mhaphungpleng/rc-car/images/PID.png

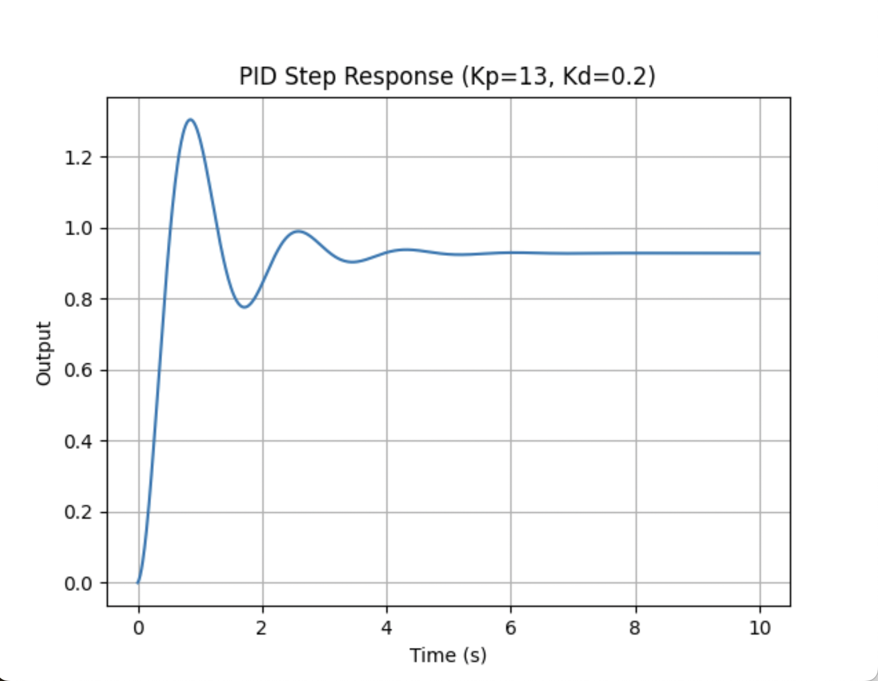
images/PID.png
