mhaphungpleng/rc-car/models/meshes/งาน6.jpg

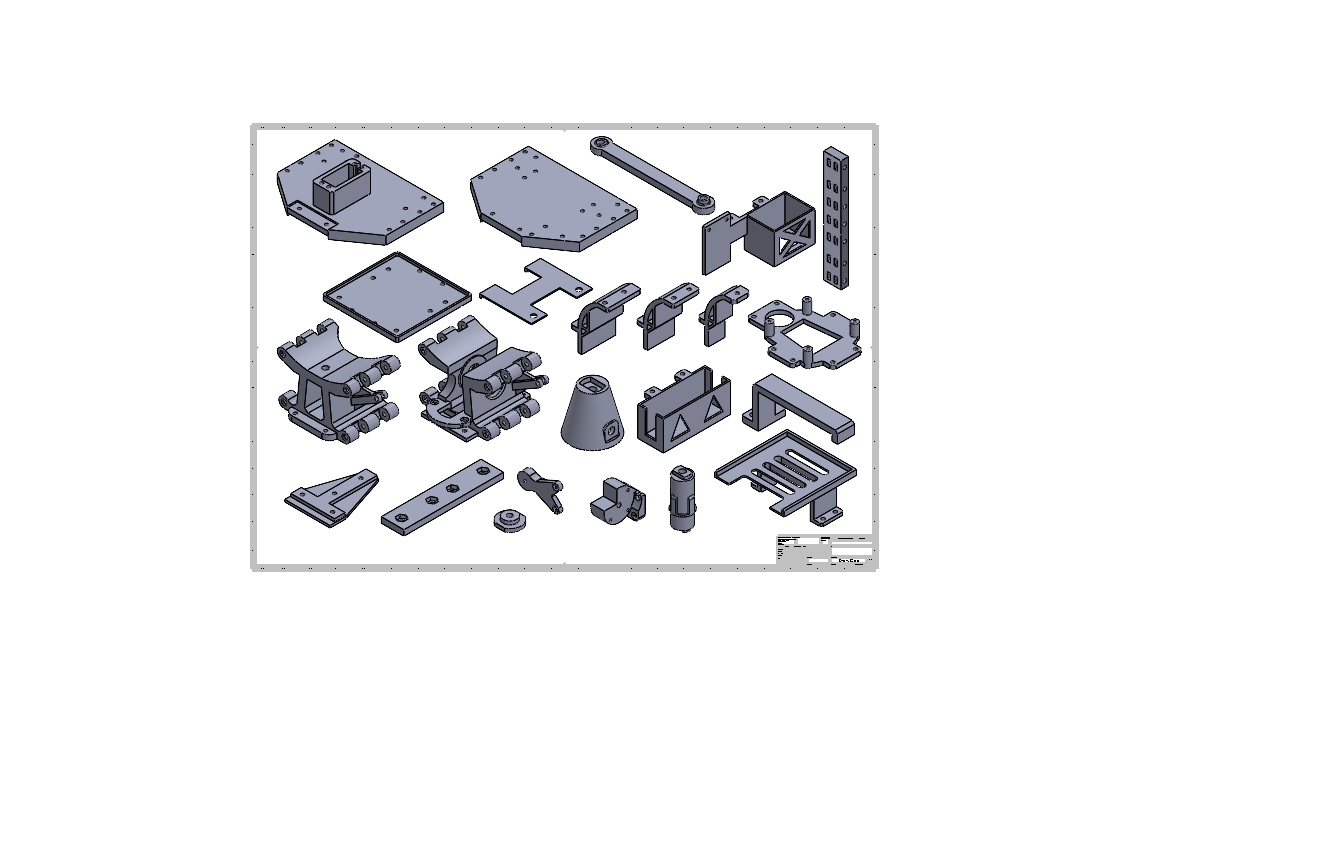
models/meshes/งาน6.jpg
