mhaphungpleng/rc-car/models/cad/BB_Base.SLDPRT

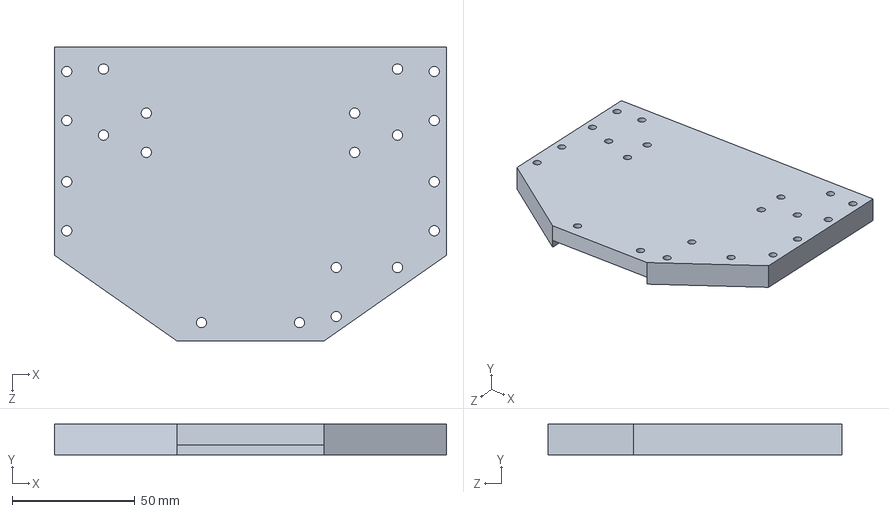
[picture p25: CAD file, 2026-02-09]
models/cad/BB_Base.SLDPRT
160.0 x 12.5 x 120.0 mm
