mhaphungpleng/rc-car/models/cad_stl/GearRccar46T.stl

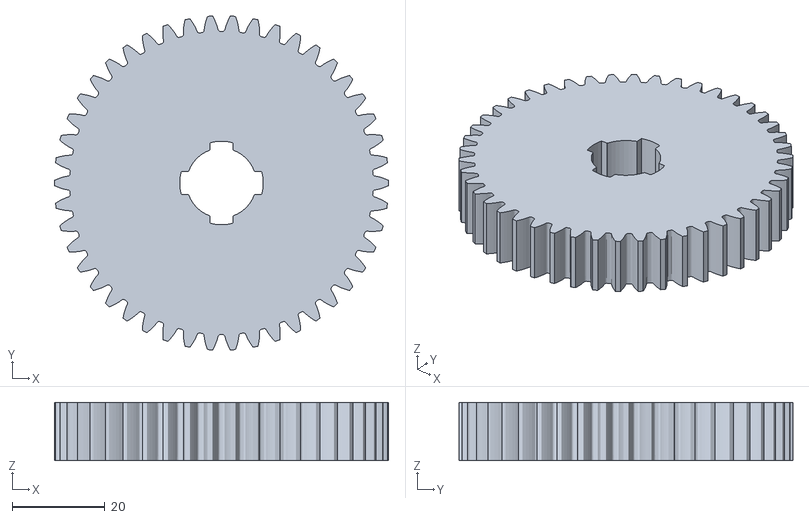
[picture p26: CAD file, 2026-02-09]
models/cad_stl/GearRccar46T.stl
72.0 x 71.9 x 12.5
