mhaphungpleng/rc-car/models/cad/Servohorn.SLDPRT

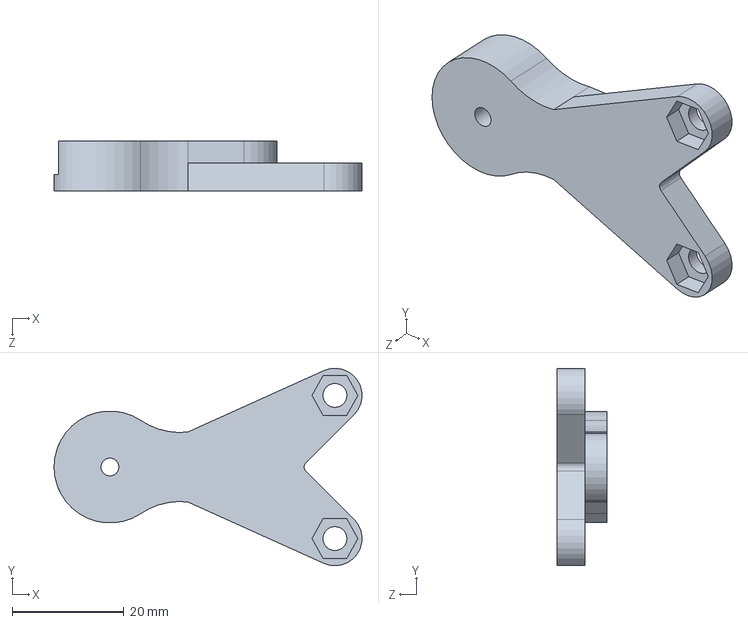
[picture p27: CAD file, 2026-02-09]
models/cad/Servohorn.SLDPRT
55.1 x 35.3 x 9.00 mm
