mhaphungpleng/rc-car/models/cad_stl/axle.stl

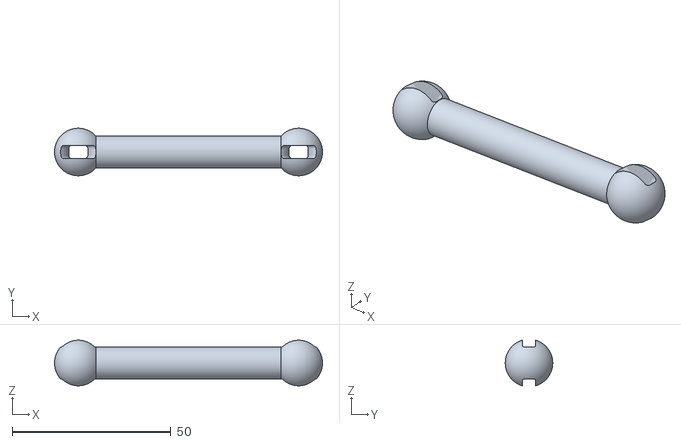
[picture p28: CAD file, 2026-02-09]
models/cad_stl/axle.stl
84.5 x 15.0 x 14.4
