mhaphungpleng/rc-car/models/cad/FFBody_to_Drive.SLDPRT

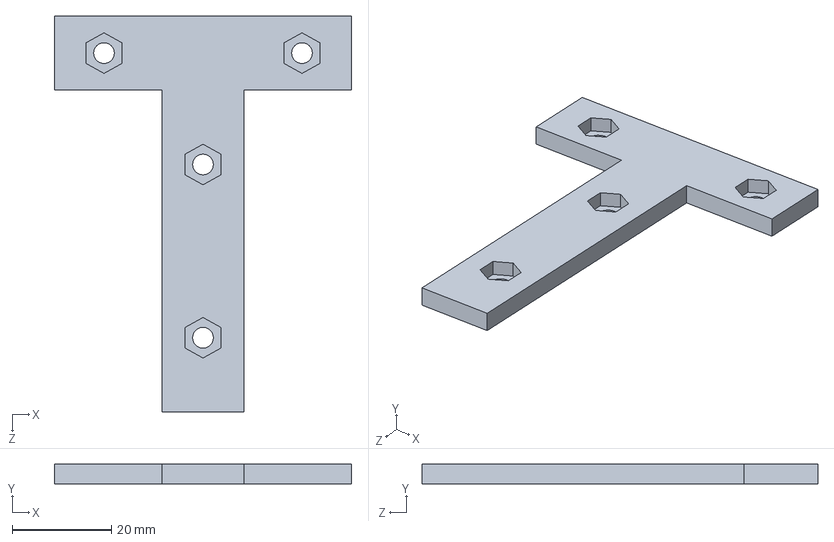
[picture p29: CAD file, 2026-02-09]
models/cad/FFBody_to_Drive.SLDPRT
60.0 x 4.00 x 80.0 mm
