mhaphungpleng/rc-car/models/cad_stl/rear_lower_fork_right.stl

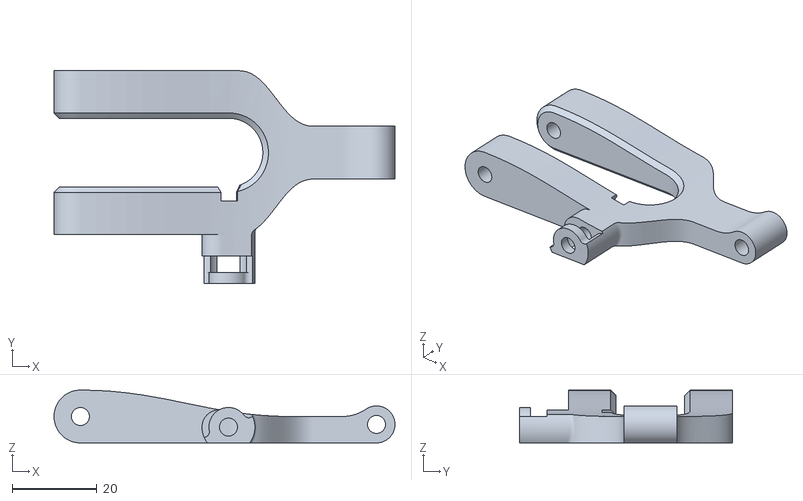
[picture p30: CAD file, 2026-02-09]
models/cad_stl/rear_lower_fork_right.stl
80.6 x 50.2 x 12.5
