mhaphungpleng/rc-car/models/cad/GearRccar52T.step

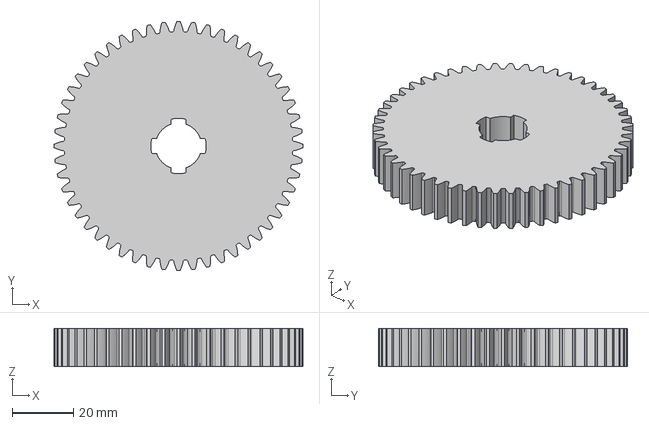
[picture p31: CAD file, 2026-02-09]
models/cad/GearRccar52T.step
81.0 x 81.0 x 12.5 mm
