mhaphungpleng/rc-car/models/cad_stl/SeizeFF.STL

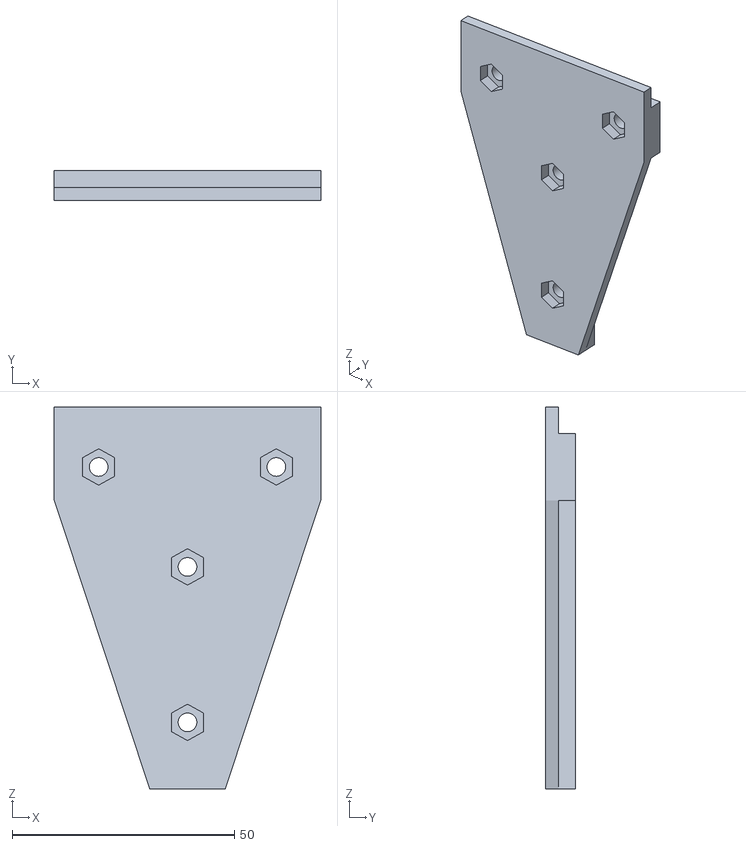
[picture p32: CAD file, 2026-02-09]
models/cad_stl/SeizeFF.STL
60.0 x 6.80 x 86.0
