mhaphungpleng/rc-car/models/cad/Futureboard.SLDPRT

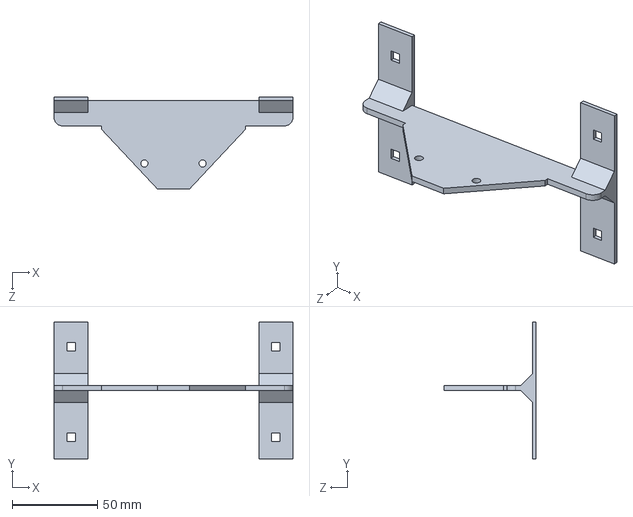
[picture p33: CAD file, 2026-02-09]
models/cad/Futureboard.SLDPRT
140.0 x 80.0 x 54.0 mm
