mhaphungpleng/rc-car/models/cad_stl/Drivengearaxel.STL

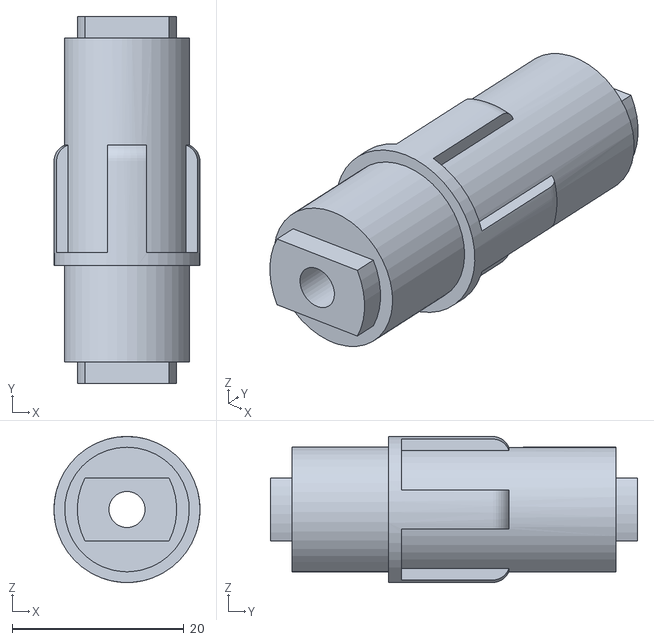
[picture p34: CAD file, 2026-02-09]
models/cad_stl/Drivengearaxel.STL
17.0 x 42.8 x 17.0
