mhaphungpleng/rc-car/models/cad/ServoarmV85.SLDPRT

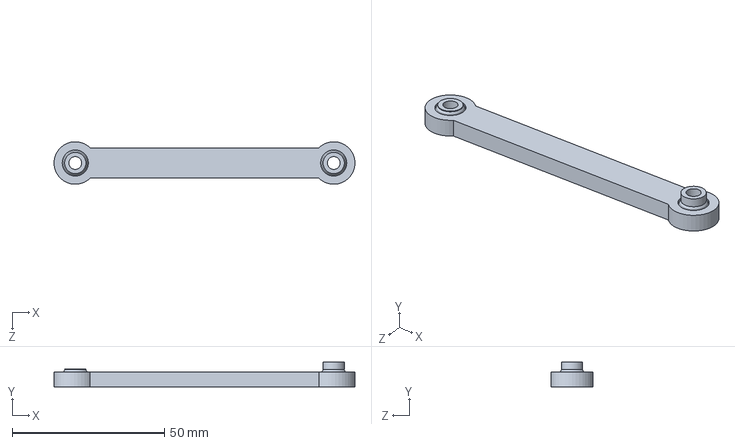
[picture p35: CAD file, 2026-02-09]
models/cad/ServoarmV85.SLDPRT
99.0 x 8.20 x 14.0 mm
