mhaphungpleng/rc-car/models/cad_stl/GearRccar42T.stl

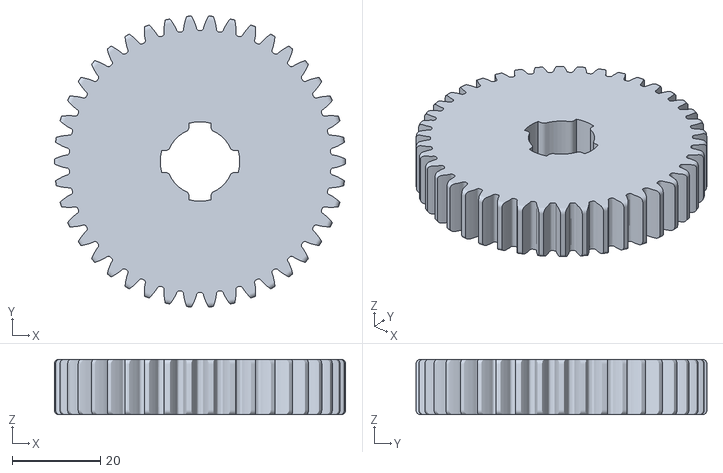
[picture p36: CAD file, 2026-02-09]
models/cad_stl/GearRccar42T.stl
66.0 x 65.9 x 12.5
