mhaphungpleng/rc-car/models/cad/LidarArmBack.SLDPRT

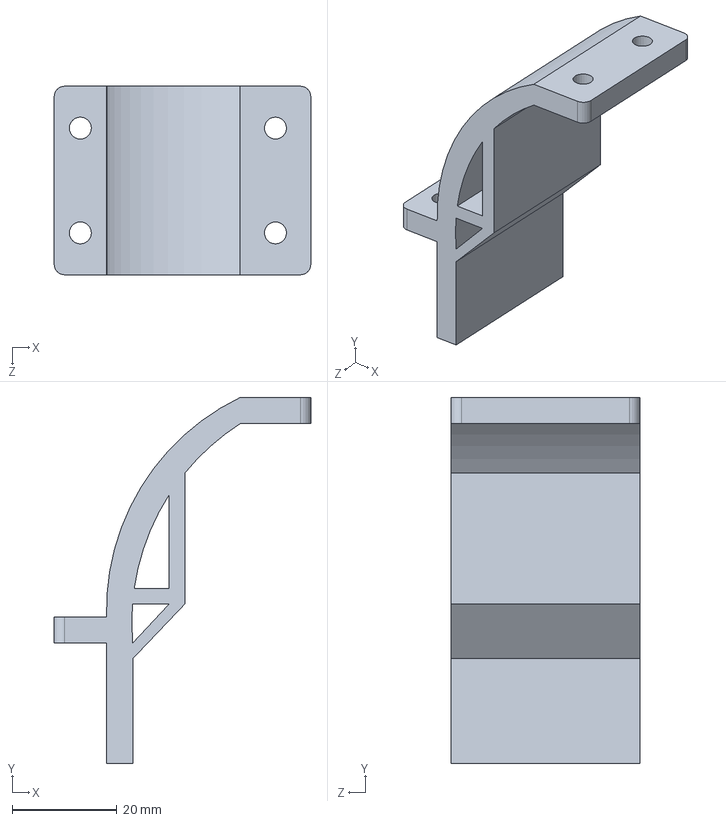
[picture p37: CAD file, 2026-02-09]
models/cad/LidarArmBack.SLDPRT
49.0 x 69.9 x 36.0 mm
