mhaphungpleng/rc-car/models/cad_stl/SeizeFHigh.STL

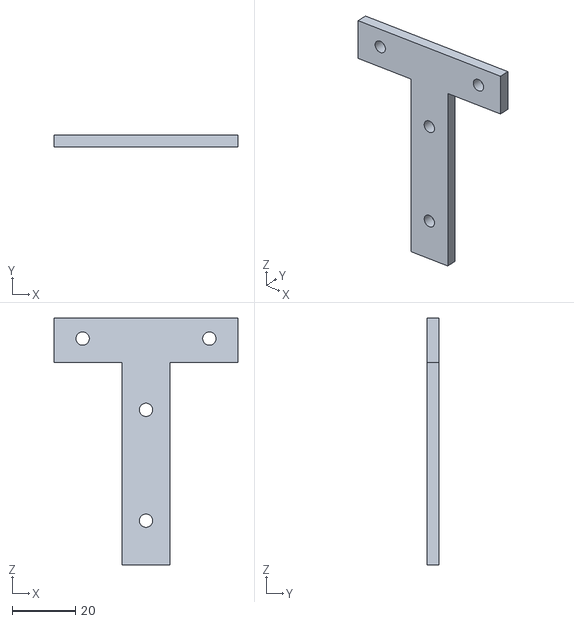
[picture p38: CAD file, 2026-02-09]
models/cad_stl/SeizeFHigh.STL
58.0 x 3.80 x 78.0
