mhaphungpleng/rc-car/models/cad/Box.SLDPRT

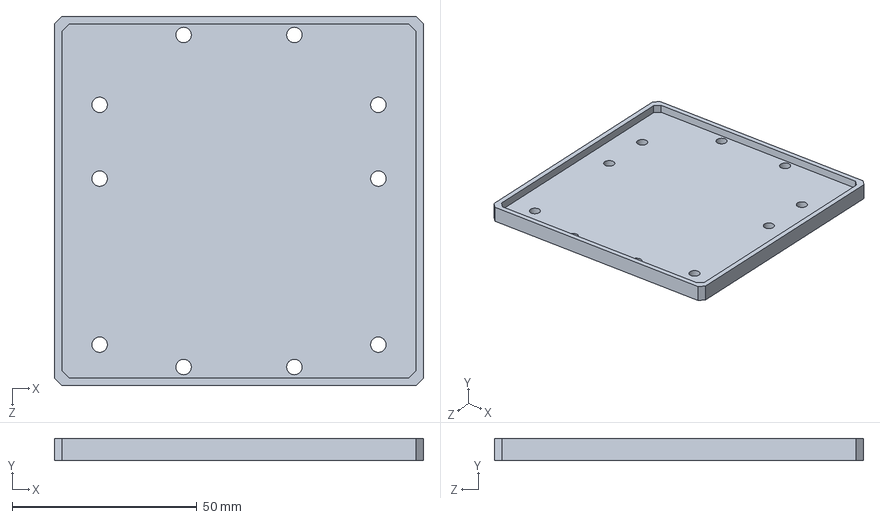
[picture p39: CAD file, 2026-02-09]
models/cad/Box.SLDPRT
100.0 x 6.00 x 100.0 mm
