mhaphungpleng/rc-car/models/cad_stl/Moter.STL

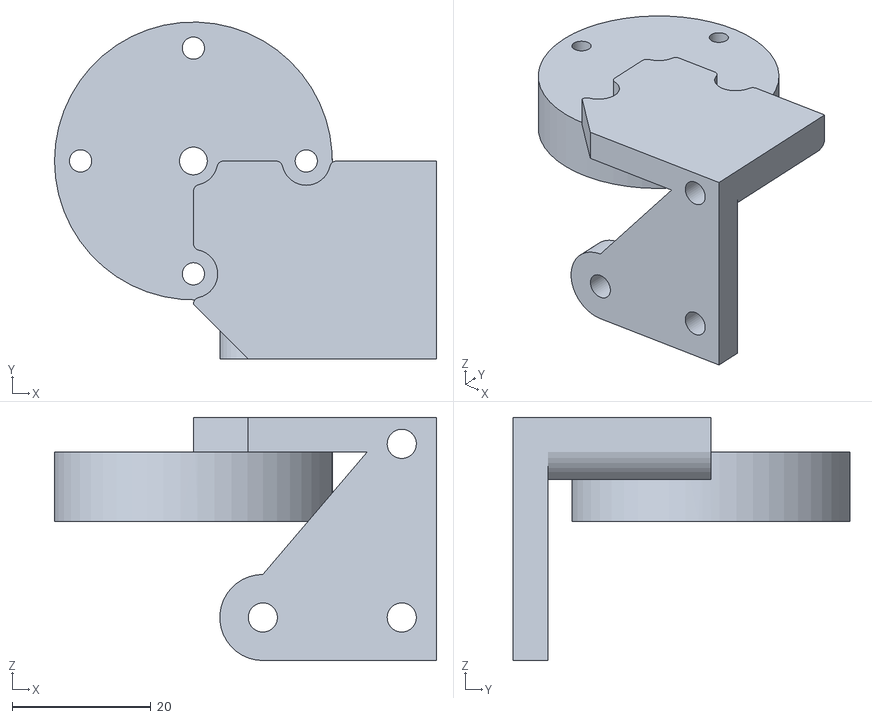
[picture p40: CAD file, 2026-02-09]
models/cad_stl/Moter.STL
55.0 x 48.5 x 35.0
