mhaphungpleng/rc-car/models/cad/Pi5_coverF.SLDPRT

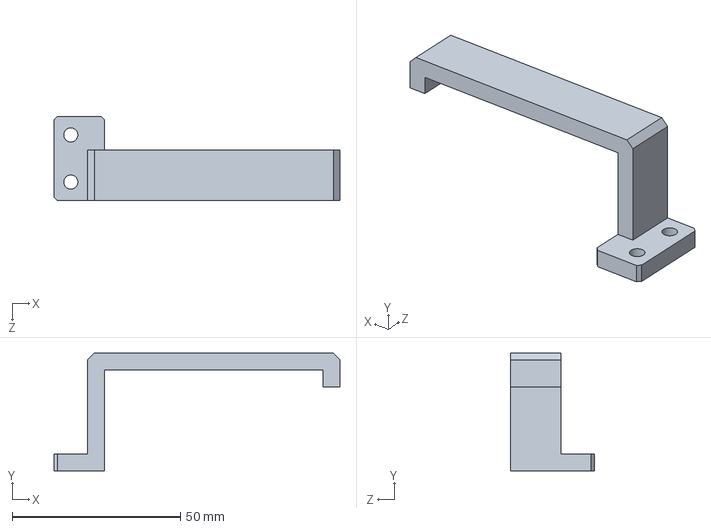
[picture p41: CAD file, 2026-02-09]
models/cad/Pi5_coverF.SLDPRT
85.0 x 35.0 x 25.0 mm
