mhaphungpleng/rc-car/models/cad_stl/ArmLidar.STL

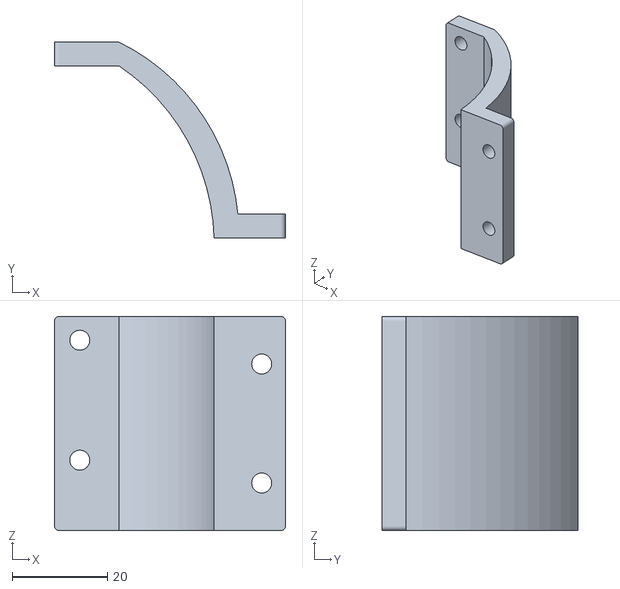
[picture p42: CAD file, 2026-02-09]
models/cad_stl/ArmLidar.STL
48.5 x 41.2 x 45.0
