mhaphungpleng/rc-car/models/cad_stl/Servoarm.STL

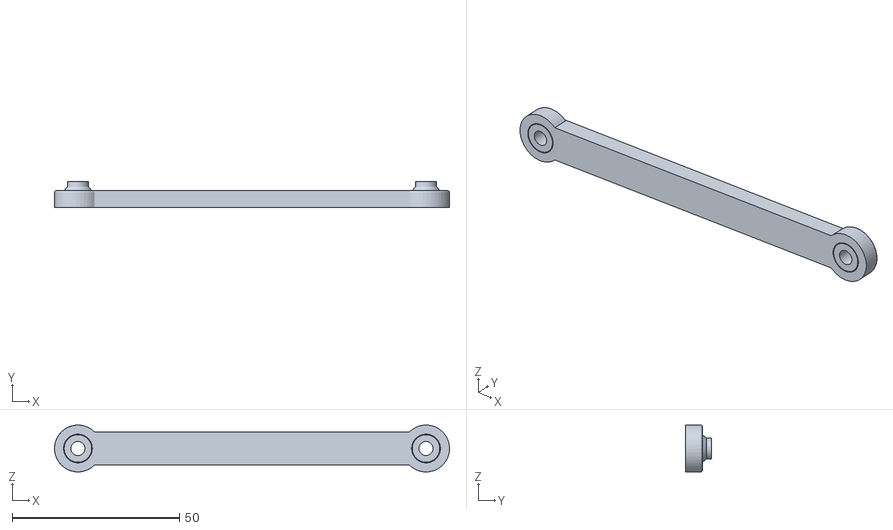
[picture p43: CAD file, 2026-02-09]
models/cad_stl/Servoarm.STL
118.0 x 7.71 x 14.0
