mhaphungpleng/rc-car/models/cad/Gyro.SLDPRT

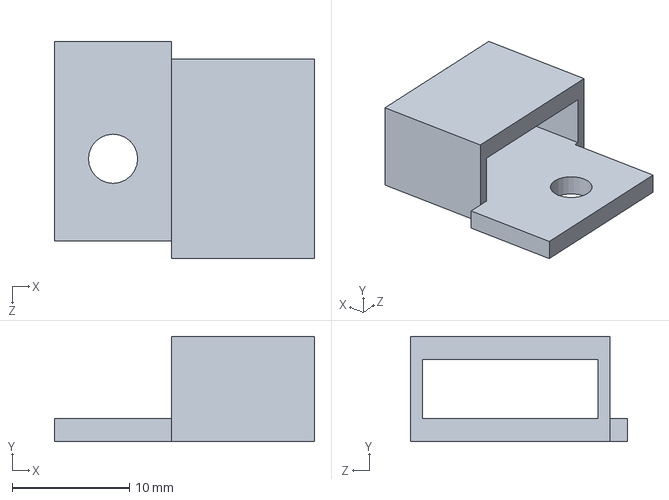
[picture p44: CAD file, 2026-02-09]
models/cad/Gyro.SLDPRT
22.2 x 9.00 x 18.5 mm
