mhaphungpleng/rc-car/models/cad_stl/rear_upper_fork.stl

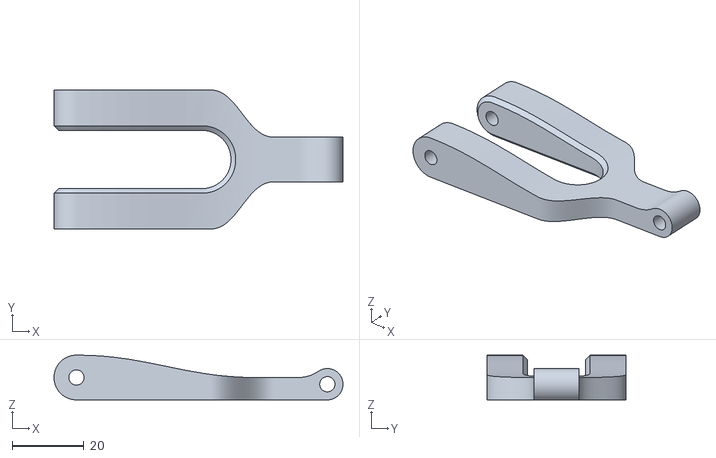
[picture p45: CAD file, 2026-02-09]
models/cad_stl/rear_upper_fork.stl
80.6 x 38.8 x 12.5
