mhaphungpleng/rc-car/models/cad/Wheel_grap6anglemm.SLDPRT

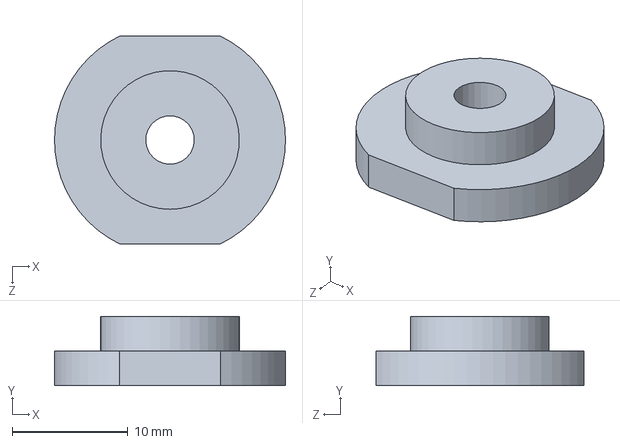
[picture p46: CAD file, 2026-02-09]
models/cad/Wheel_grap6anglemm.SLDPRT
20.0 x 6.00 x 18.0 mm
