mhaphungpleng/rc-car/models/cad_stl/SeizeB.STL

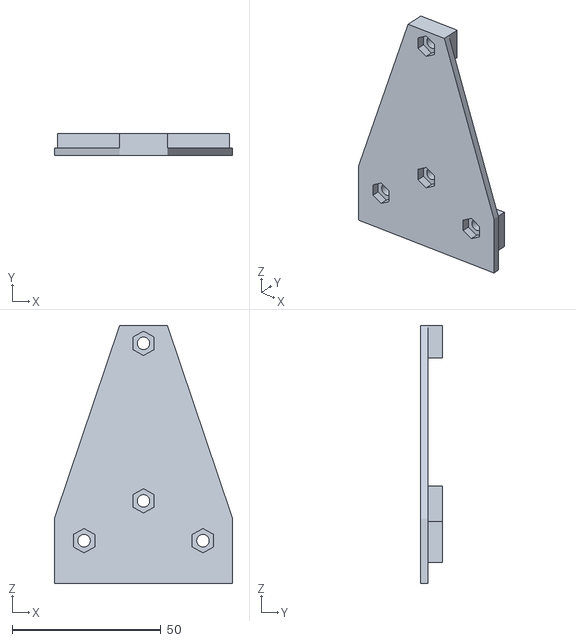
[picture p47: CAD file, 2026-02-09]
models/cad_stl/SeizeB.STL
60.0 x 7.30 x 86.8
