mhaphungpleng/rc-car/models/cad/SpoilerCover.SLDPRT

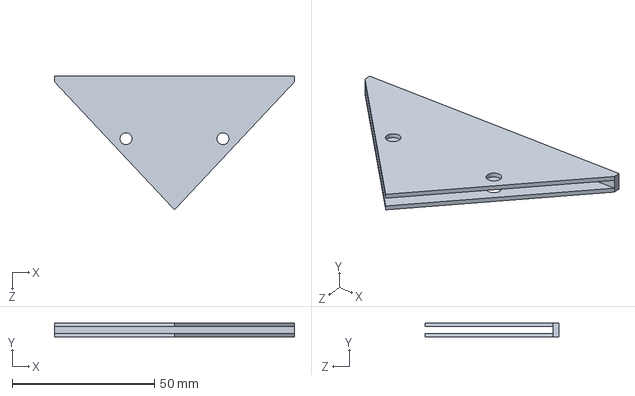
[picture p48: CAD file, 2026-02-09]
models/cad/SpoilerCover.SLDPRT
84.3 x 4.80 x 47.0 mm
