mhaphungpleng/rc-car/models/cad/Spoiler.SLDPRT

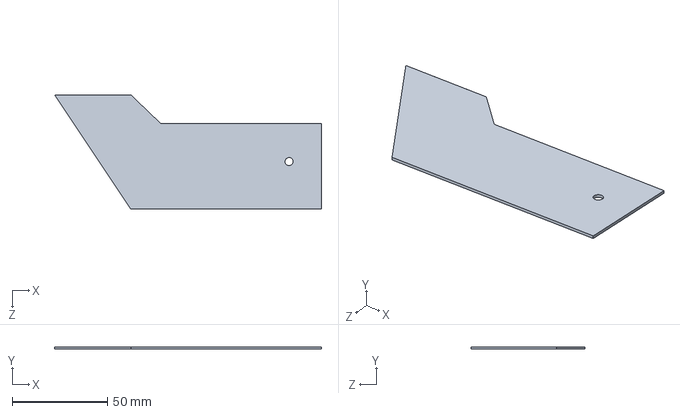
[picture p49: CAD file, 2026-02-09]
models/cad/Spoiler.SLDPRT
140.0 x 1.20 x 60.0 mm
