mhaphungpleng/rc-car/models/cad/BatteryV2.SLDPRT

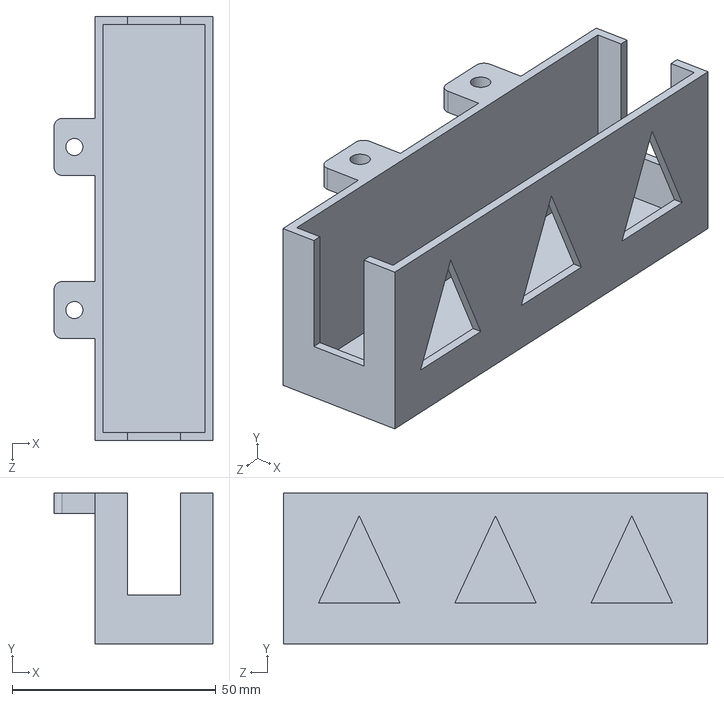
[picture p50: CAD file, 2026-02-09]
models/cad/BatteryV2.SLDPRT
39.0 x 37.0 x 104.0 mm
