mhaphungpleng/rc-car/models/cad/LidarArmR.SLDPRT

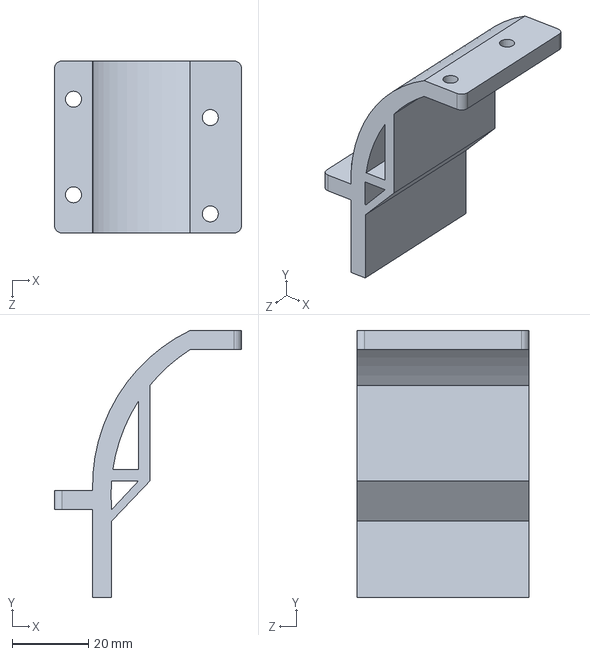
[picture p51: CAD file, 2026-02-09]
models/cad/LidarArmR.SLDPRT
49.0 x 69.9 x 45.0 mm
