mhaphungpleng/rc-car/models/cad/Driven_axel.SLDPRT

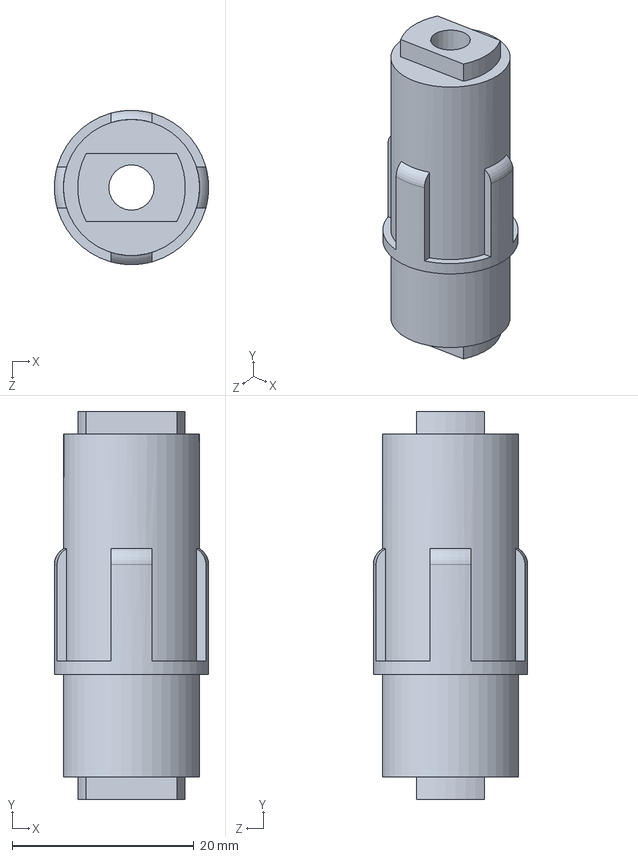
[picture p52: CAD file, 2026-02-09]
models/cad/Driven_axel.SLDPRT
17.0 x 42.8 x 17.0 mm
