mhaphungpleng/rc-car/models/cad/Battery.SLDPRT

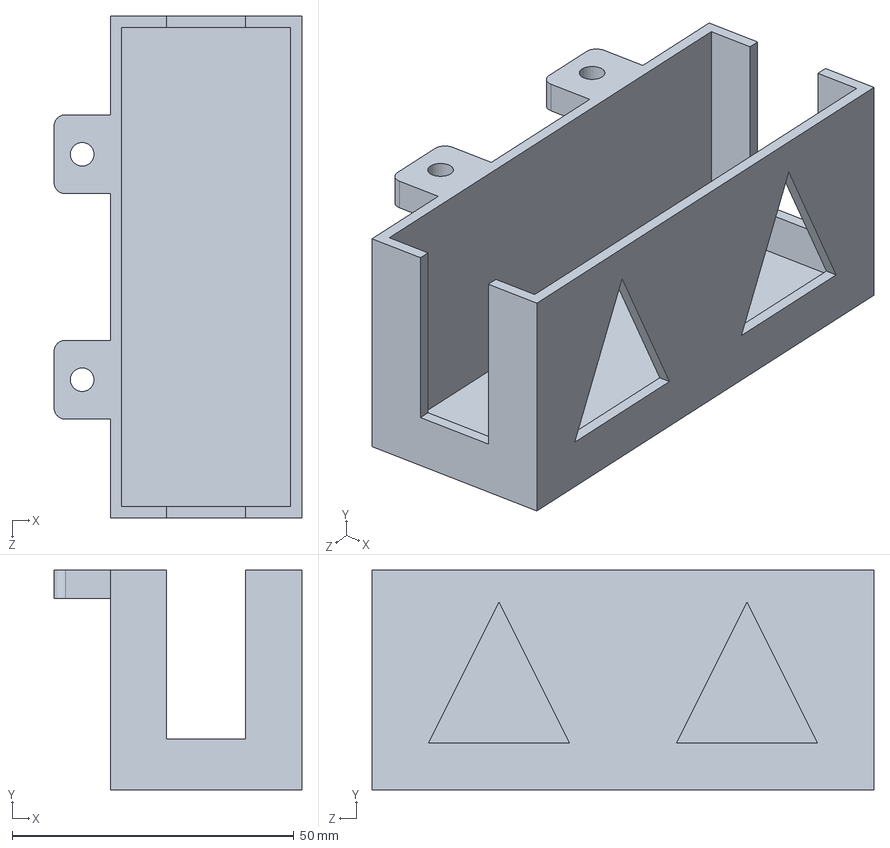
[picture p53: CAD file, 2026-02-09]
models/cad/Battery.SLDPRT
44.0 x 39.0 x 89.0 mm
