mhaphungpleng/rc-car/models/cad/Lidar.SLDPRT

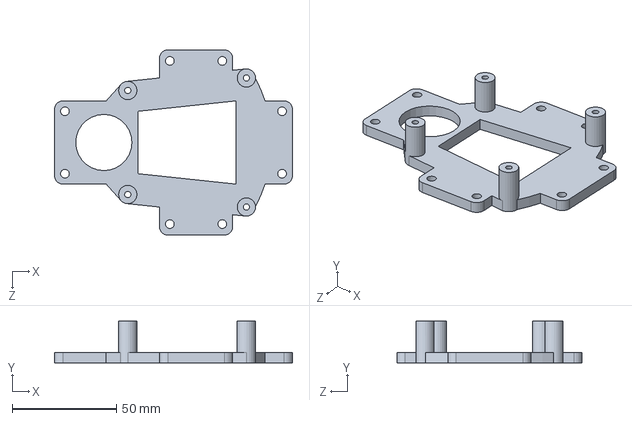
[picture p54: CAD file, 2026-02-09]
models/cad/Lidar.SLDPRT
114.4 x 20.0 x 89.0 mm
