mhaphungpleng/rc-car/models/cad/BoxBigSize.SLDPRT

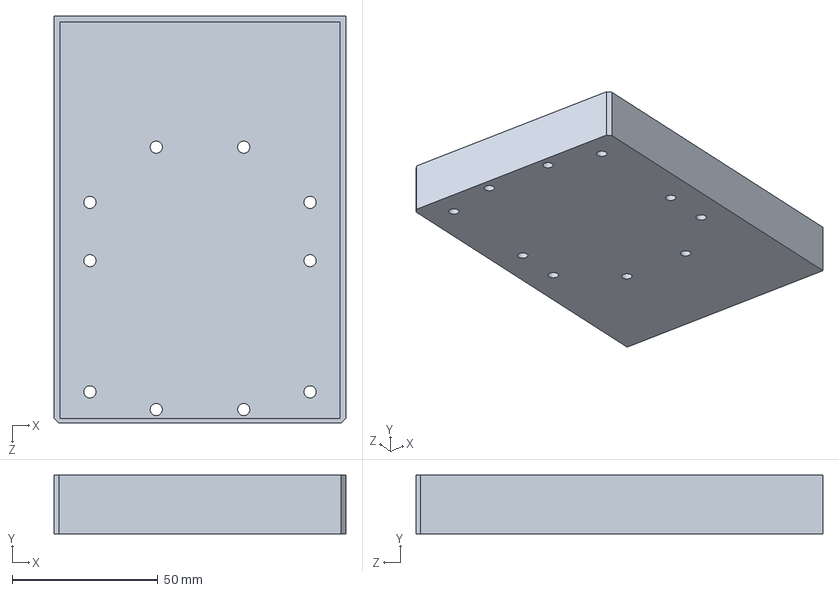
[picture p55: CAD file, 2026-02-09]
models/cad/BoxBigSize.SLDPRT
100.0 x 20.1 x 139.6 mm
