mhaphungpleng/rc-car/models/cad/BBDrive_BaseV82.SLDPRT

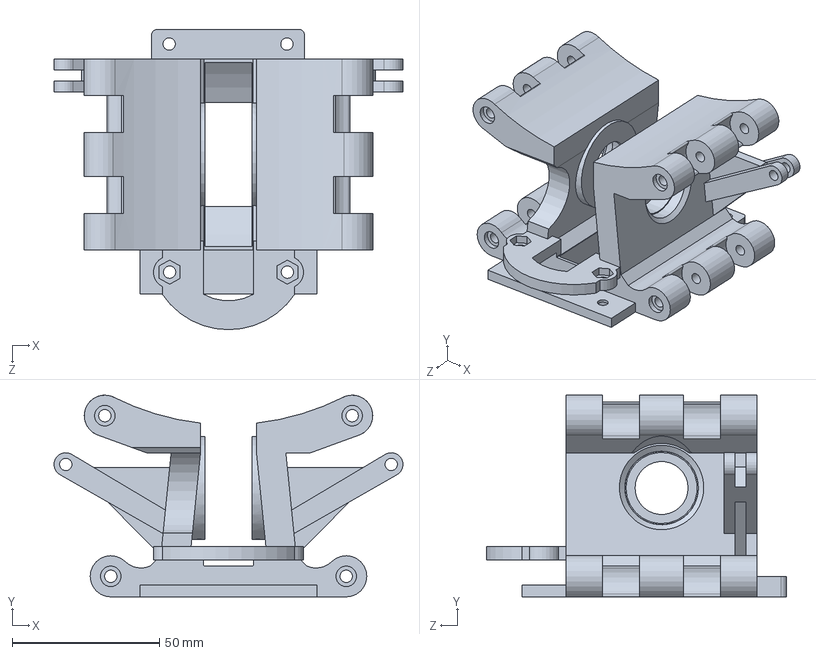
[picture p56: CAD file, 2026-02-09]
models/cad/BBDrive_BaseV82.SLDPRT
118.6 x 68.6 x 102.0 mm
