mhaphungpleng/rc-car/models/cad/GearRccar6T.step

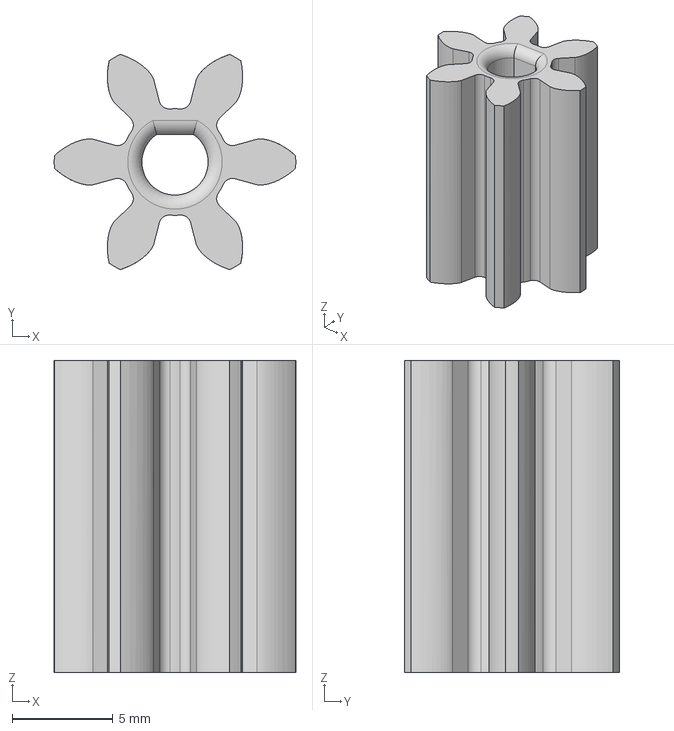
[picture p57: CAD file, 2026-02-09]
models/cad/GearRccar6T.step
12.0 x 10.7 x 15.5 mm
