mhaphungpleng/rc-car/models/cad/Supportbody.SLDPRT

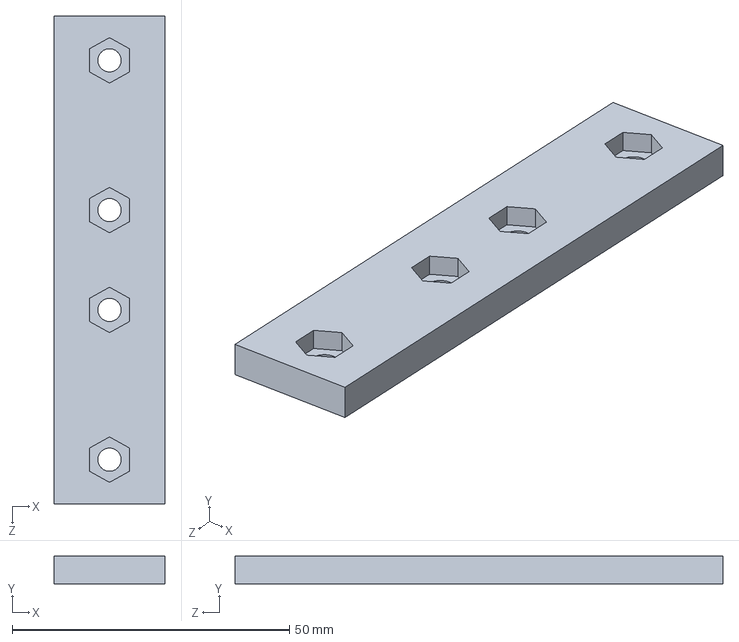
[picture p58: CAD file, 2026-02-09]
models/cad/Supportbody.SLDPRT
20.0 x 5.00 x 88.0 mm
