mhaphungpleng/rc-car/models/cad/Radio.SLDPRT

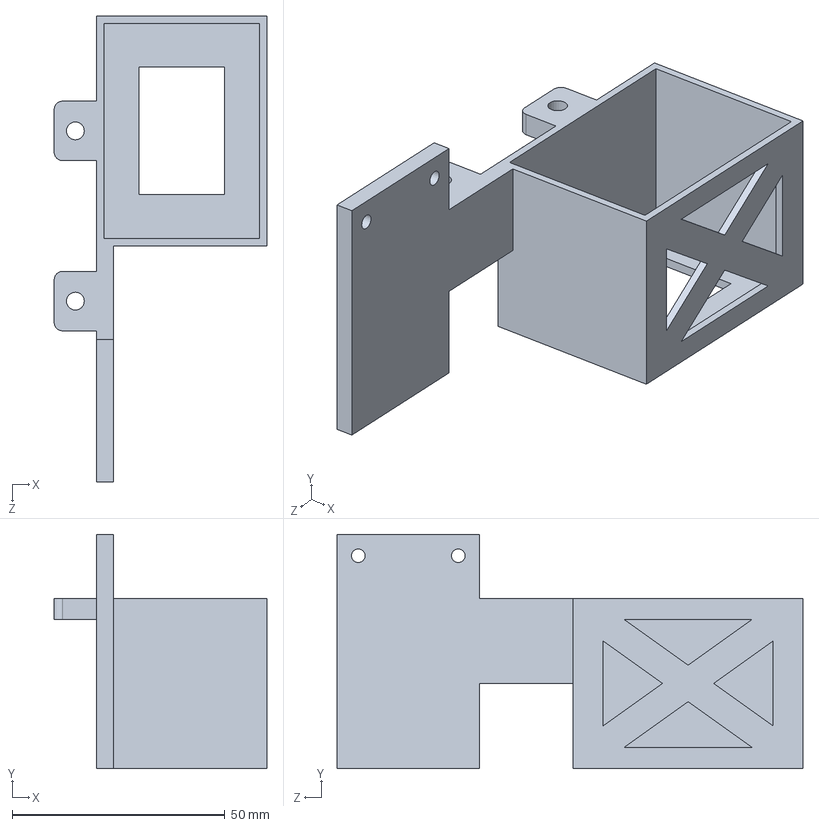
[picture p59: CAD file, 2026-02-09]
models/cad/Radio.SLDPRT
50.0 x 55.0 x 109.5 mm
