mhaphungpleng/rc-car/models/cad/Pi5_coverB.SLDPRT

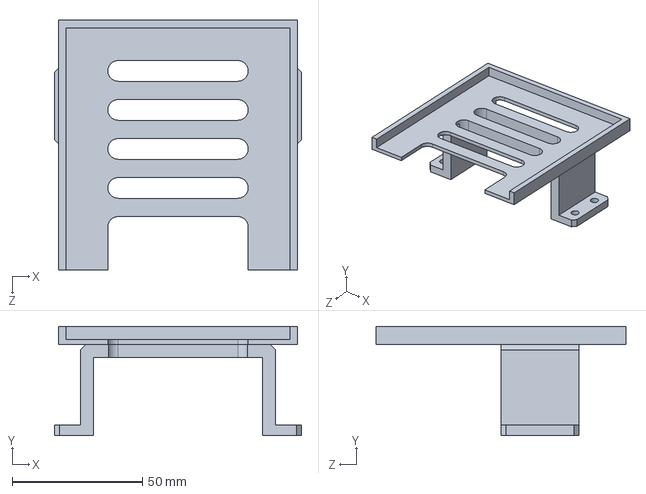
[picture p60: CAD file, 2026-02-09]
models/cad/Pi5_coverB.SLDPRT
95.0 x 42.0 x 96.0 mm
