mhaphungpleng/rc-car/models/cad/CoverJoint_in.SLDPRT

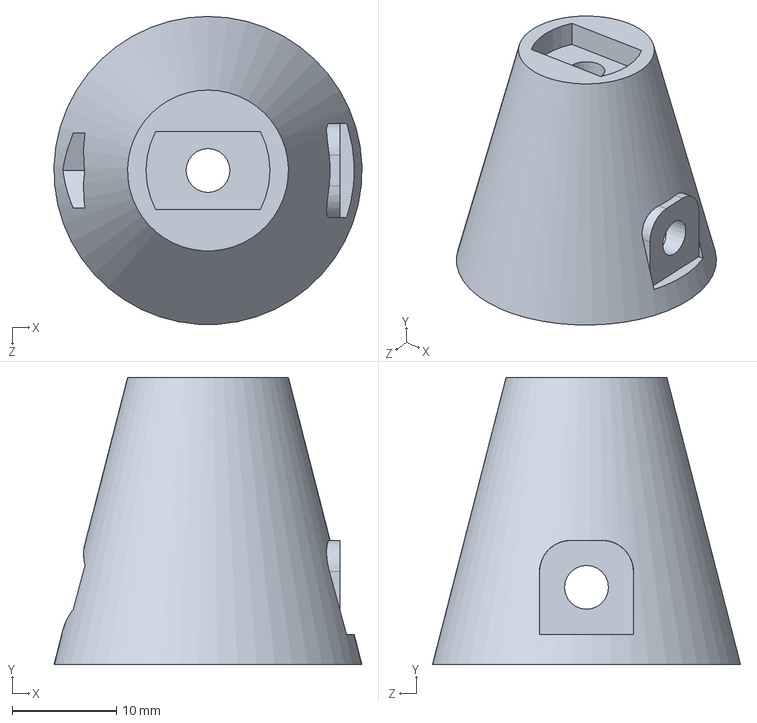
[picture p61: CAD file, 2026-02-09]
models/cad/CoverJoint_in.SLDPRT
29.5 x 27.5 x 29.5 mm
