mhaphungpleng/rc-car/models/cad/LidarArmMiddle.SLDPRT

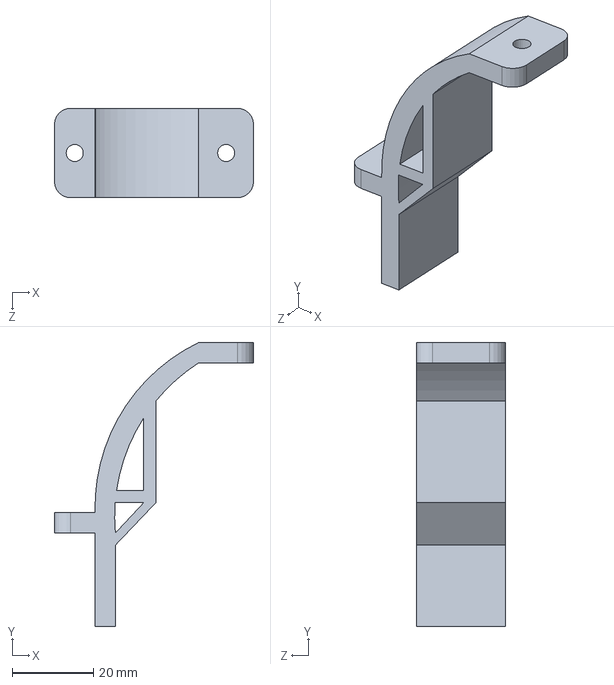
[picture p62: CAD file, 2026-02-09]
models/cad/LidarArmMiddle.SLDPRT
49.0 x 69.9 x 22.0 mm
