mhaphungpleng/rc-car/models/cad/Body_sideL.SLDPRT

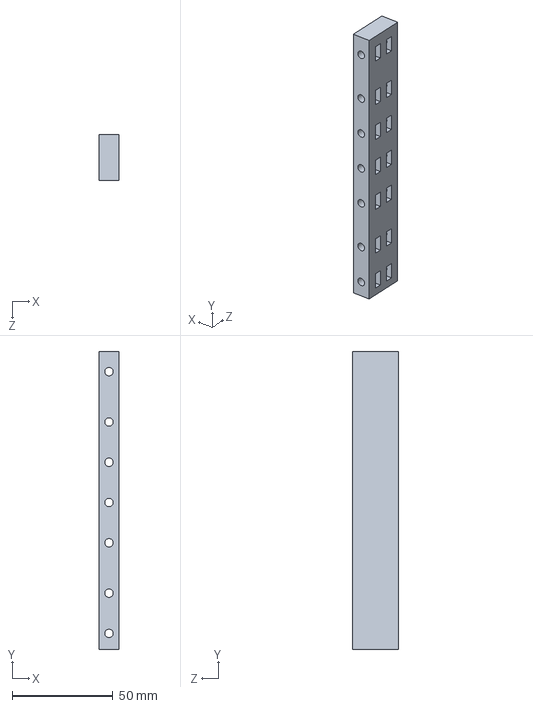
[picture p63: CAD file, 2026-02-09]
models/cad/Body_sideL.SLDPRT
10.00 x 148.0 x 23.0 mm
