mhaphungpleng/rc-car/images/hardware_setup.png

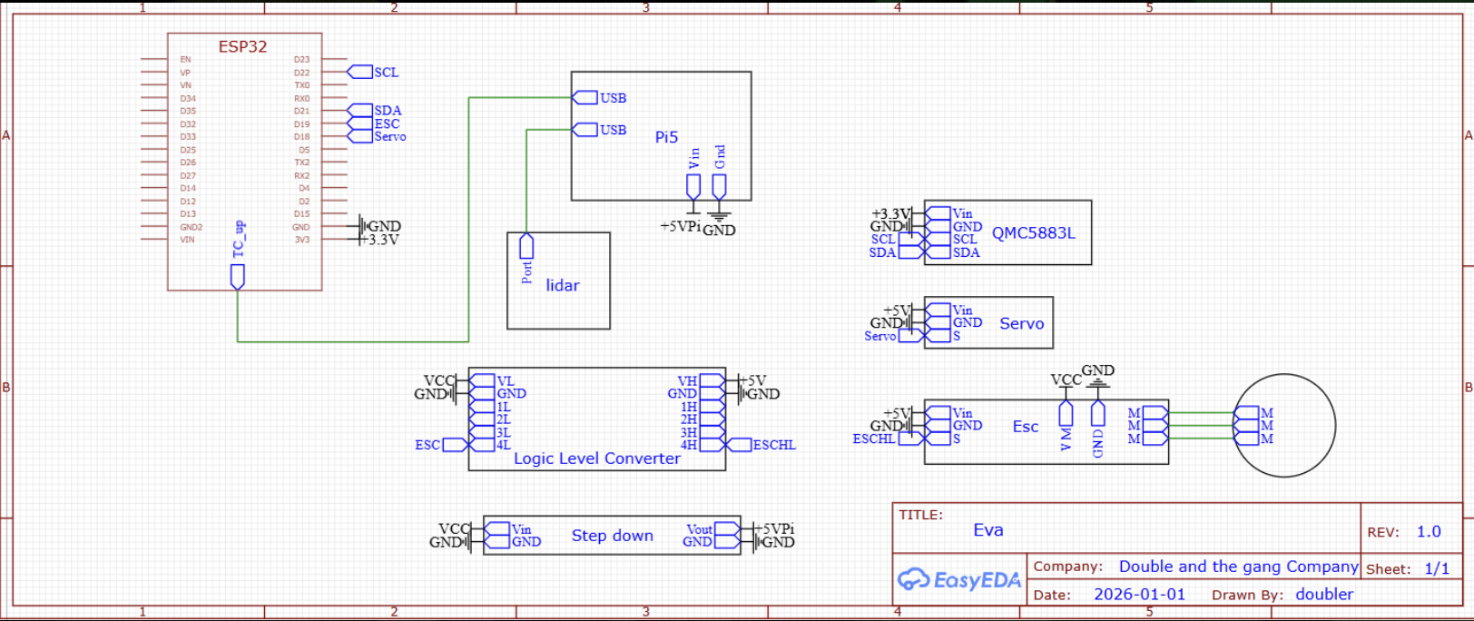
images/hardware_setup.png
